loganma02/Light-Jacket/PCB/Light_Jacket_rev0_2/Light_Jacket_rev0_2 2.png

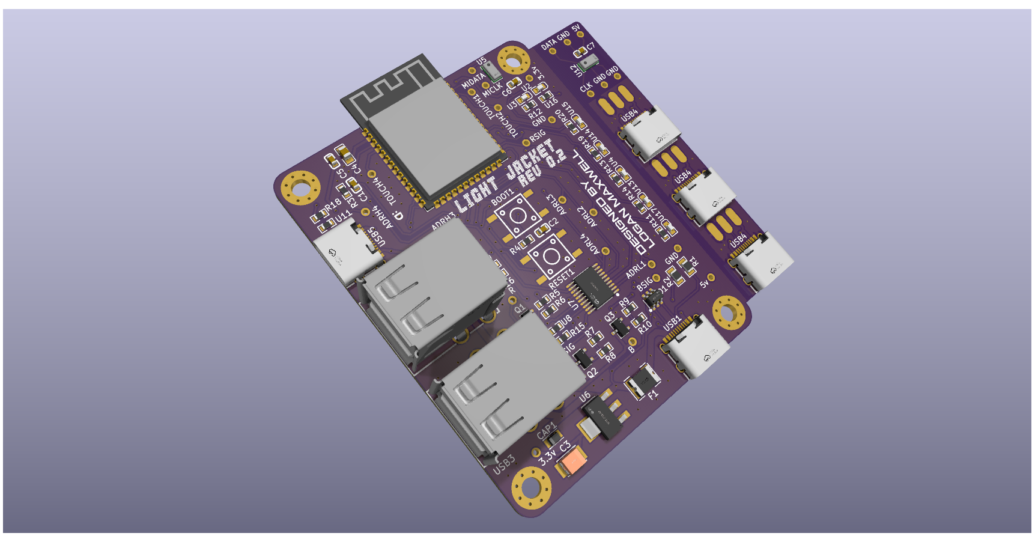
PCB/Light_Jacket_rev0_2/Light_Jacket_rev0_2 2.png
