loganma02/Light-Jacket/PCB/Light_Jacket_rev0_2/Light_Jacket_rev0_2 - Mousebites.png

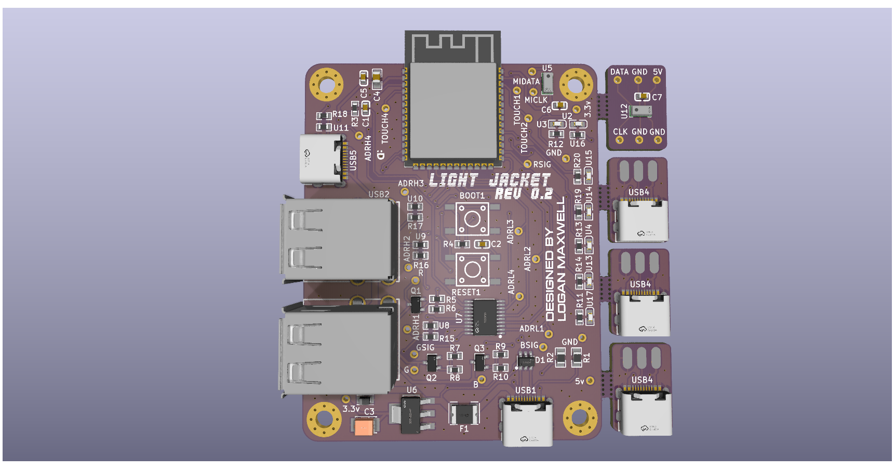
PCB/Light_Jacket_rev0_2/Light_Jacket_rev0_2 - Mousebites.png
