loganma02/Light-Jacket/PCB/Light_Jacket_rev0_2/EASYEDA_MODELS/C0805_L2.0-W1.3-H1.3.step

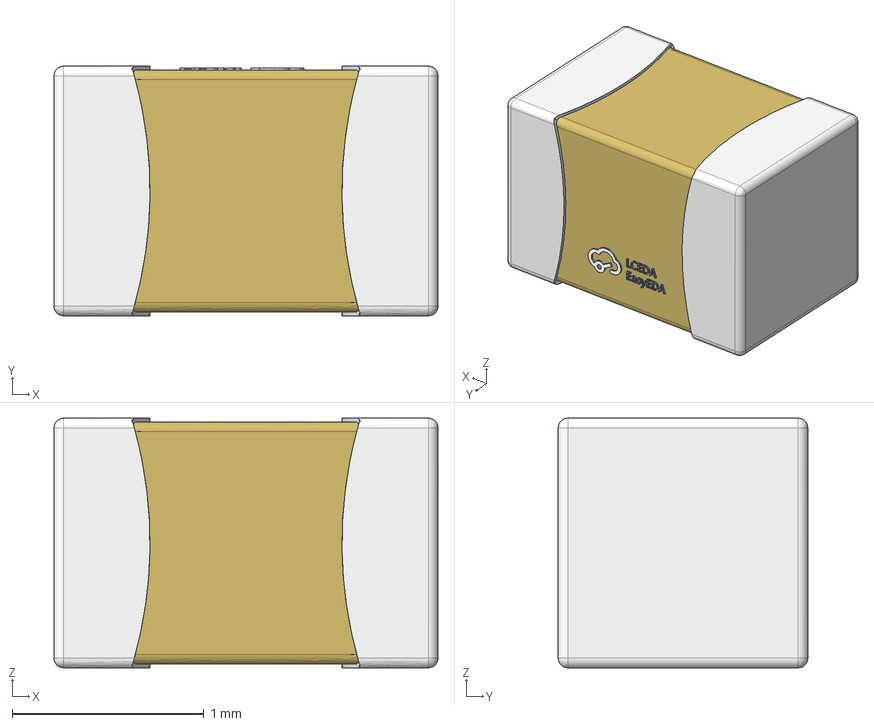
[picture p41: CAD file, 2026-04-22]
PCB/Light_Jacket_rev0_2/EASYEDA_MODELS/C0805_L2.0-W1.3-H1.3.step
2.00 x 1.30 x 1.30 mm
