loganma02/Light-Jacket/PCB/Light_Jacket_rev0_2/EASYEDA_MODELS/USB-A-TH_AF-SS-JB17.6.step

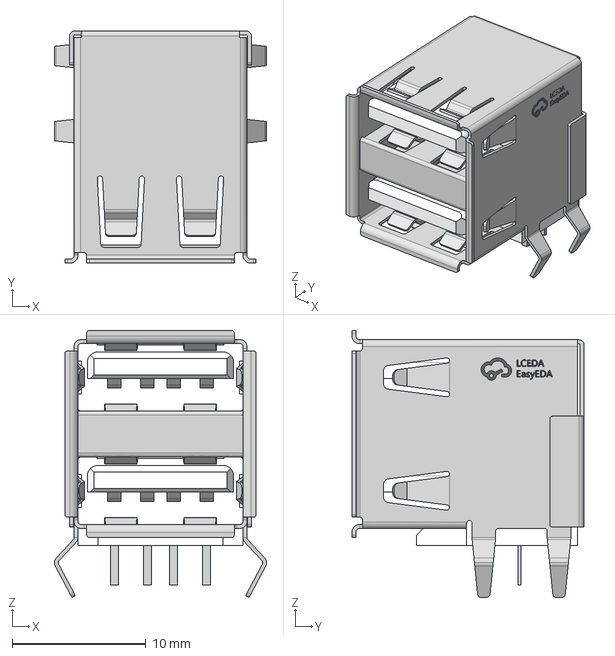
[picture p42: CAD file, 2026-04-22]
PCB/Light_Jacket_rev0_2/EASYEDA_MODELS/USB-A-TH_AF-SS-JB17.6.step
15.9 x 17.4 x 20.0 mm
